jemtech/ILDA/hardware/kicad/OpAmps.sch

## KiCad design hardware/kicad/OpAmps.sch (2015-08-31, an earlier design)

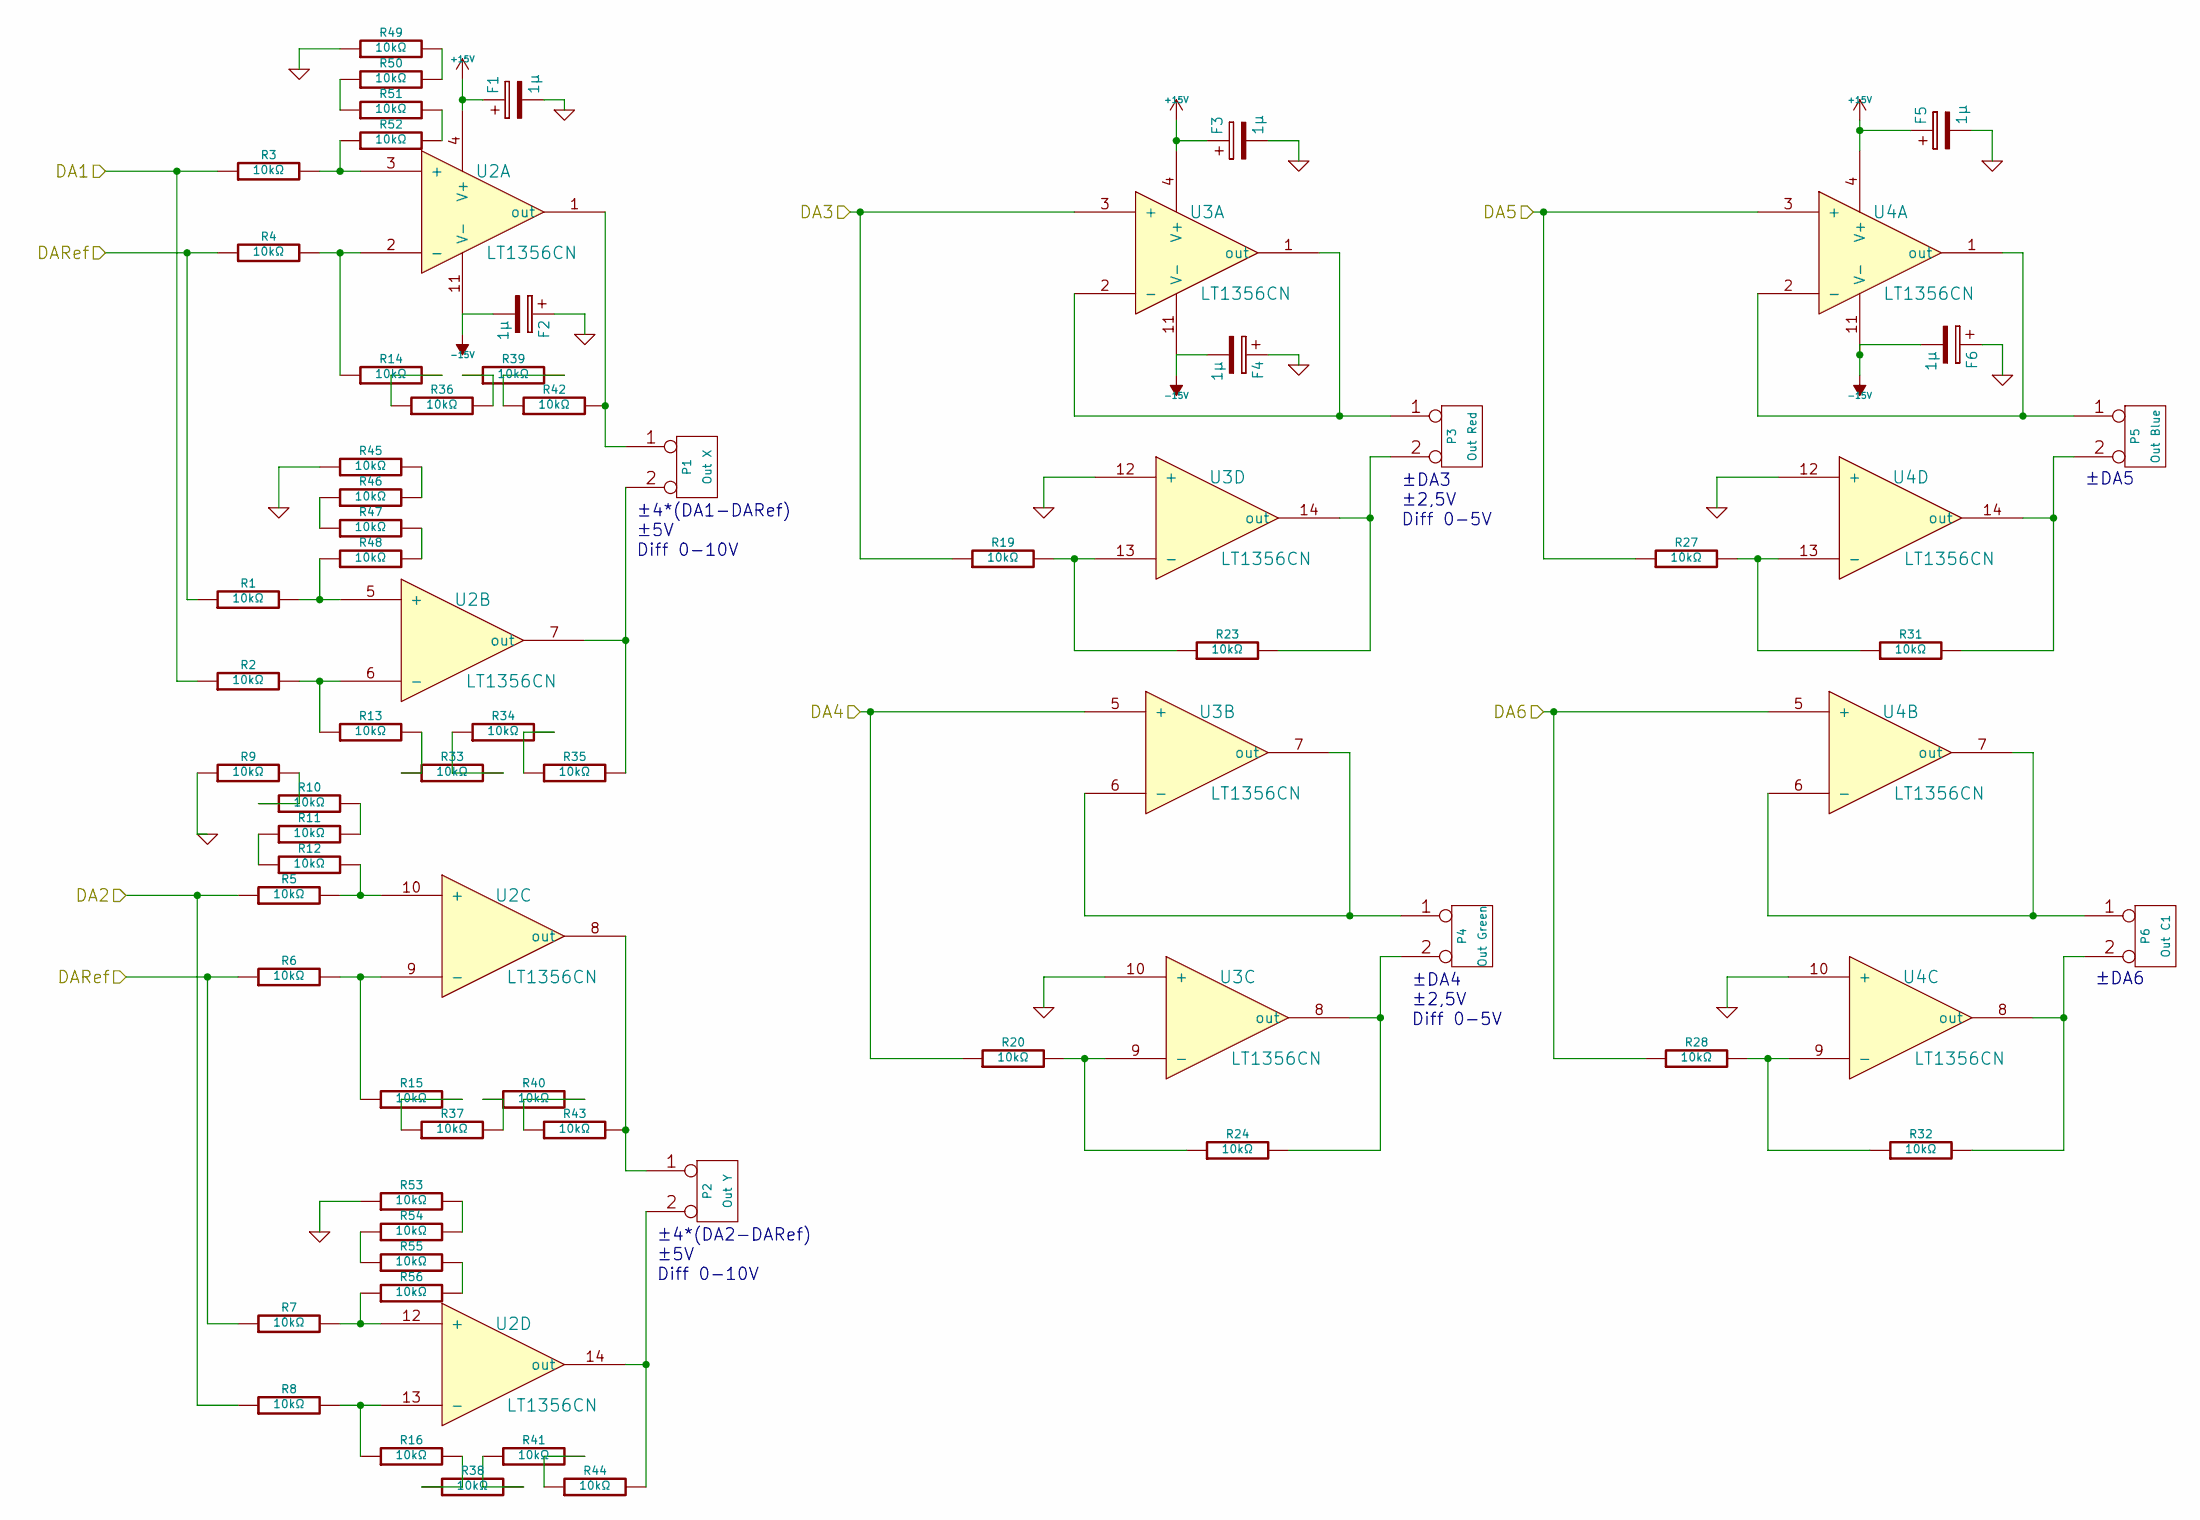
[picture p4: schematic OpAmps.sch]

Parts:
F1, F2, F3, F4, F5, F6: 1µ; TantalC_SizeB_EIA-3528_HandSoldering
P1: Out X
P2: Out Y
P3: Out Red
P4: Out Green
P5: Out Blue
P6: Out C1
R1, R2, R3, R4, R5, R6, R7, R8, R9, R10, R11, R12, R13, R14, R15, R16, R20, R24, R33, R34, R35, R36, R37, R38, R39, R40, R41, R42, R43, R44, R45, R46, R47, R48, R49, R50, R51, R52, R53, R54, R55, R56: 10kΩ; R_0603_HandSoldering
R19, R23, R27, R28, R31, R32: 10kΩ
U2, U3, U4: LT1356CN

Connections:
+15V: F1.1, F3.1, F5.1, U2.4 (V+), U3.4 (V+), U4.4 (V+)
-15V: F2.2, F4.2, F6.2, U2.11 (V-), U3.11 (V-), U4.11 (V-)
DA1: R2.1, R3.1
DA2: R5.1, R8.1
DA3: R19.1, U3.3 (+)
DA4: R20.1, U3.5 (+)
DA5: R27.1, U4.3 (+)
DA6: R28.1, U4.5 (+)
DARef: R1.1, R4.1, R6.1, R7.1
GND: F1.2, F2.1, F3.2, F4.1, F5.2, F6.1, R9.1, R45.1, R49.1, R53.1, U3.10 (+), U3.12 (+), U4.10 (+), U4.12 (+)
unnamed: P1.1, R42.2, U2.1 (out)
unnamed: P1.2 (PM), R35.2, U2.7 (out)
unnamed: P2.1, R43.2, U2.8 (out)
unnamed: P2.2 (PM), R44.2, U2.14 (out)
unnamed: P3.1, U3.1 (out), U3.2 (-)
unnamed: P3.2 (PM), R23.2, U3.14 (out)
unnamed: P4.1, U3.6 (-), U3.7 (out)
unnamed: P4.2 (PM), R24.2, U3.8 (out)
unnamed: P5.1, U4.1 (out), U4.2 (-)
unnamed: P5.2 (PM), R31.2, U4.14 (out)
unnamed: P6.1, U4.6 (-), U4.7 (out)
unnamed: P6.2 (PM), R32.2, U4.8 (out)
unnamed: R1.2, R48.1, U2.5 (+)
unnamed: R3.2, R52.1, U2.3 (+)
unnamed: R9.2, R10.1
unnamed: R10.2, R11.2
unnamed: R11.1, R12.1
unnamed: R5.2, R12.2, U2.10 (+)
unnamed: R2.2, R13.1, U2.6 (-)
unnamed: R13.2, R33.1
unnamed: R4.2, R14.1, U2.2 (-)
unnamed: R14.2, R36.1
unnamed: R6.2, R15.1, U2.9 (-)
unnamed: R15.2, R37.1
unnamed: R8.2, R16.1, U2.13 (-)
unnamed: R16.2, R38.1
unnamed: R19.2, R23.1, U3.13 (-)
unnamed: R20.2, R24.1, U3.9 (-)
unnamed: R27.2, R31.1, U4.13 (-)
unnamed: R28.2, R32.1, U4.9 (-)
unnamed: R33.2, R34.1
unnamed: R34.2, R35.1
unnamed: R36.2, R39.1
unnamed: R37.2, R40.1
unnamed: R38.2, R41.1
unnamed: R39.2, R42.1
unnamed: R40.2, R43.1
unnamed: R41.2, R44.1
unnamed: R45.2, R46.2
unnamed: R46.1, R47.1
unnamed: R47.2, R48.2
unnamed: R49.2, R50.2
unnamed: R50.1, R51.1
unnamed: R51.2, R52.2
unnamed: R53.2, R54.2
unnamed: R54.1, R55.1
unnamed: R55.2, R56.2
unnamed: R7.2, R56.1, U2.12 (+)

Notes on the sheet:
±4*(DA1-DARef) ±5V Diff 0-10V
±4*(DA2-DARef) ±5V Diff 0-10V
±DA3 ±2,5V Diff 0-5V
±DA4 ±2,5V Diff 0-5V
±DA5
±DA6
