jemtech/ILDA/hardware/kicad/ildagenerator.sch

## KiCad design hardware/kicad/ildagenerator.sch (2015-08-31, an earlier design)

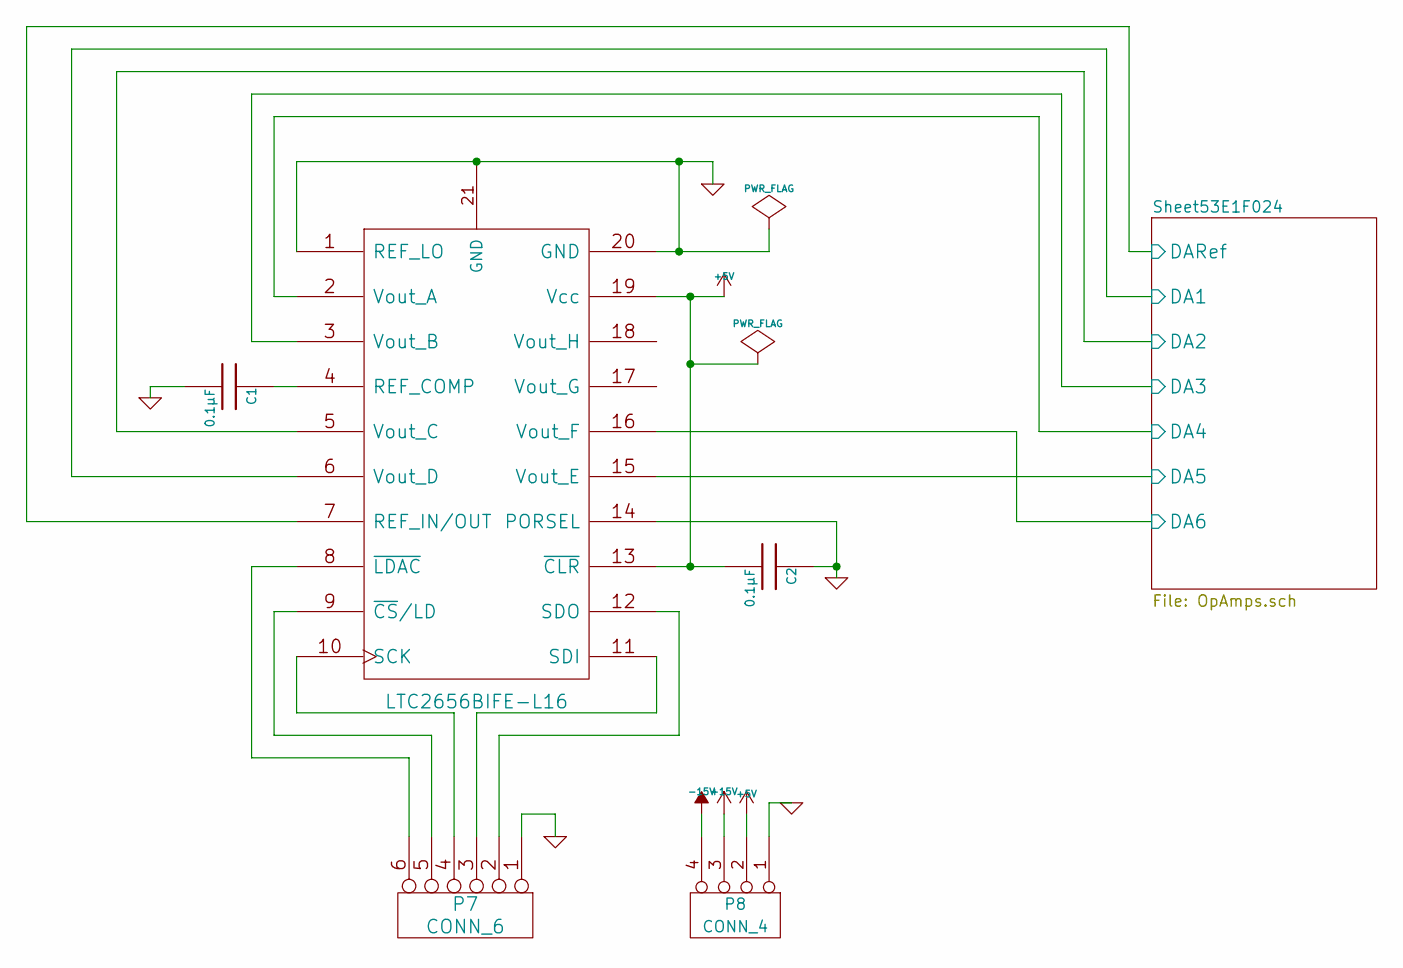
[picture p5: schematic ildagenerator.sch]

Parts:
C1, C2: 0.1µF; C_0805_HandSoldering
P7: CONN_6
P8: CONN_4
U1: LTC2656BIFE-L16

Connections:
+5V: C2.2, P8.2, U1.13 (~CLR), U1.19 (Vcc)
+15V: P8.3
-15V: P8.4
DA1: U1.6 (Vout_D)
DA2: U1.5 (Vout_C)
DA3: U1.3 (Vout_B)
DA4: U1.2 (Vout_A)
DA5: U1.15 (Vout_E)
DA6: U1.16 (Vout_F)
DARef: U1.7 (REF_IN/OUT)
GND: C1.2, C2.1, P7.1, P8.1, U1.1 (REF_LO), U1.14 (PORSEL), U1.20 (GND), U1.21 (GND)
unnamed: C1.1, U1.4 (REF_COMP)
unnamed: P7.2, U1.12 (SDO)
unnamed: P7.3, U1.11 (SDI)
unnamed: P7.4, U1.10 (SCK)
unnamed: P7.5, U1.9 (~CS~/LD)
unnamed: P7.6, U1.8 (~LDAC)
