jemtech/ILDA/software/raspberrypi/ildaFile.h

#ifndef ILDAFILE_H
#define ILDAFILE_H

#define PARSE_STATE_SEARCHING_HEADER 0
#define PARSE_STATE_PARSING_HEADER 1

#define ILDA_3D_COORD_HEADER_TYPE 0x00
#define ILDA_2D_COORD_HEADER_TYPE 0x01
#define ILDA_COLOUR_PALETTE_HEADER_TYPE 0x02
#define ILDA_3D_COORD_TRUE_COL_HEADER_TYPE 0x04
#define ILDA_2D_COORD_TRUE_COL_HEADER_TYPE 0x05
static const char HEADER_START[] = {'I','L','D','A',0x00,0x00,0x00};

/*
Execute this function to parse a ILDA-formated file and run its commands
*/
void executeIldaFileByName(char fileName[], char loop);

// ilda standard color palette (r,g,b)
static const unsigned char ILDA_DEFAULT_COLOUR_PALETTE[256][3]={
{ 0, 0, 0 }, // Black/blanked (fixed)
{ 255, 255, 255 }, // White (fixed)
{ 255, 0, 0 }, // Red (fixed)
{ 255, 255, 0 }, // Yellow (fixed)
{ 0, 255, 0 }, // Green (fixed)
{ 0, 255, 255 }, // Cyan (fixed)
{ 0, 0, 255 }, // Blue (fixed)
{ 255, 0, 255 }, // Magenta (fixed)
{ 255, 128, 128 }, // Light red
{ 255, 140, 128 },
{ 255, 151, 128 },
{ 255, 163, 128 },
{ 255, 174, 128 },
{ 255, 186, 128 },
{ 255, 197, 128 },
{ 255, 209, 128 },
{ 255, 220, 128 },
{ 255, 232, 128 },
{ 255, 243, 128 },
{ 255, 255, 128 }, // Light yellow
{ 243, 255, 128 },
{ 232, 255, 128 },
{ 220, 255, 128 },
{ 209, 255, 128 },
{ 197, 255, 128 },
{ 186, 255, 128 },
{ 174, 255, 128 },
{ 163, 255, 128 },
{ 151, 255, 128 },
{ 140, 255, 128 },
{ 128, 255, 128 }, // Light green
{ 128, 255, 140 },
{ 128, 255, 151 },
{ 128, 255, 163 },
{ 128, 255, 174 },
{ 128, 255, 186 },
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
{ 203, 203, 203 },
{ 192, 192, 192 }, // Light gray (3/4 intensity)
{ 181, 181, 181 },
{ 171, 171, 171 },
{ 160, 160, 160 }, // Medium-light gray (5/8 int.)
{ 149, 149, 149 },
{ 139, 139, 139 },
{ 128, 128, 128 }, // Medium gray (1/2 intensity)
{ 117, 117, 117 },
{ 107, 107, 107 },
{ 96, 96, 96 }, // Medium-dark gray (3/8 int.)
{ 85, 85, 85 },
{ 75, 75, 75 },
{ 64, 64, 64 }, // Dark gray (1/4 intensity)
{ 53, 53, 53 },
{ 43, 43, 43 },
{ 32, 32, 32 }, // Very dark gray (1/8 intensity)
{ 21, 21, 21 },
{ 11, 11, 11 },
{ 0, 0, 0 } // Black
};

#endif /*ILDAFILE_H*/
